Workshopshed/Dragon/3DModels/Knight.png

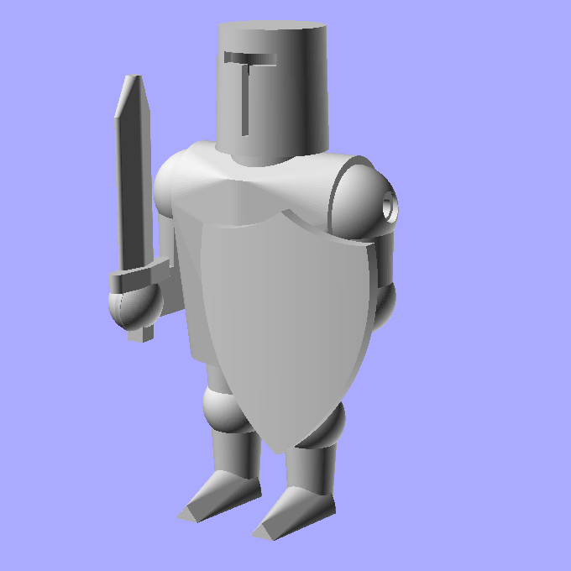
3DModels/Knight.png
