Workshopshed/Dragon/3DModels/LEDCarrier.png

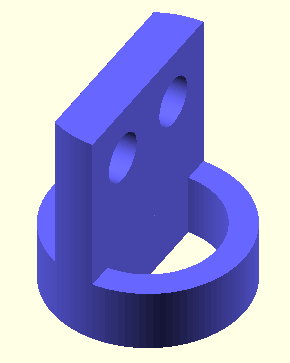
3DModels/LEDCarrier.png
