Workshopshed/Dragon/TestCode/CaptureOutput2016-05-19T205313.679536.jpg

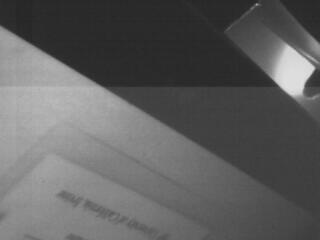
TestCode/CaptureOutput2016-05-19T205313.679536.jpg
