Workshopshed/Dragon/TestCode/Dragon.png

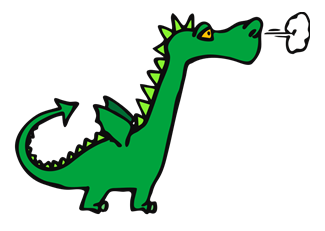
TestCode/Dragon.png
