Workshopshed/Dragon/TestCode/TestDragons1.jpg

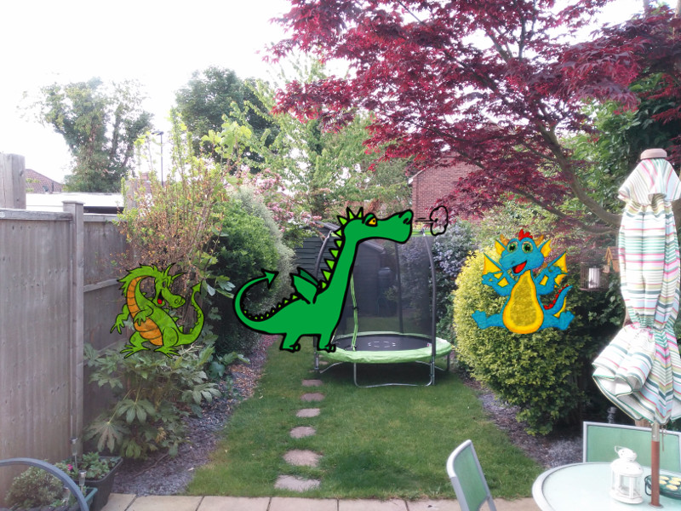
TestCode/TestDragons1.jpg
