Workshopshed/Dragon/TestCode/TestOutput2016-05-19T194859.359171.jpg

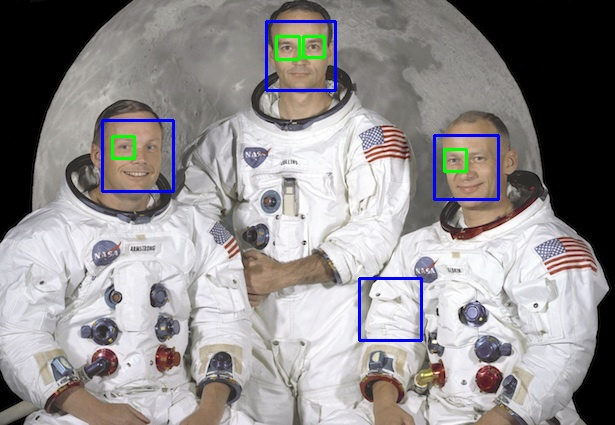
TestCode/TestOutput2016-05-19T194859.359171.jpg
