Workshopshed/Dragon/TestCode/ReadInput.py

# Test different options

while True:
    val = raw_input("Enter 1,2,3")
    print val
    if val == "1":
        print "First position"
    if val == "2":
        print "Second position"
    if val == "3":
        print "Third position"
